makestuff/lx9/lx9.sch

## KiCad design lx9.sch (2014-03-03)

Schematic: lx9.sch

Parts:
C1, C2, C3, C4, C5, C7, C8, C13, C14, C15, C16, C17, C18, C19, C20, C21, C22, C23, C24, C25, C26, C27, C28, C29, C30, C31: C
C6, C9, C10, C11, C12: CP1
CONN1: SD-CARD
CONN2: MS-EDGE80
CONN3: USB
CONN4: MS-EDGE36
J1, J2, J3: CONN_2
J4: CONN_3
R1, R2, R3, R4, R5, R6, R7, R8, R9, R10, R11, R12: R
REG1: REG3.3
REG2: REG1.2
TP1: CLK
TP2: FLAGA
TP3: PROG
TP4: DONE
U1: XC6SLX9-TQ144
U2: CY7C68014A-56PVXC
U3: IS42S16400-TSOP54
U4: '128
U5: M25P40
XTAL1: XTAL
